great-houk/mouse-project/mouse/max32625-rs/src/clkman/sys_clk_ctrl_10_i2cs.rs

#[doc = "Register `SYS_CLK_CTRL_10_I2CS` reader"]
pub struct R(crate::R<SYS_CLK_CTRL_10_I2CS_SPEC>);
impl core::ops::Deref for R {
    type Target = crate::R<SYS_CLK_CTRL_10_I2CS_SPEC>;
    #[inline(always)]
    fn deref(&self) -> &Self::Target {
        &self.0
    }
}
impl From<crate::R<SYS_CLK_CTRL_10_I2CS_SPEC>> for R {
    #[inline(always)]
    fn from(reader: crate::R<SYS_CLK_CTRL_10_I2CS_SPEC>) -> Self {
        R(reader)
    }
}
#[doc = "Register `SYS_CLK_CTRL_10_I2CS` writer"]
pub struct W(crate::W<SYS_CLK_CTRL_10_I2CS_SPEC>);
impl core::ops::Deref for W {
    type Target = crate::W<SYS_CLK_CTRL_10_I2CS_SPEC>;
    #[inline(always)]
    fn deref(&self) -> &Self::Target {
        &self.0
    }
}
impl core::ops::DerefMut for W {
    #[inline(always)]
    fn deref_mut(&mut self) -> &mut Self::Target {
        &mut self.0
    }
}
impl From<crate::W<SYS_CLK_CTRL_10_I2CS_SPEC>> for W {
    #[inline(always)]
    fn from(writer: crate::W<SYS_CLK_CTRL_10_I2CS_SPEC>) -> Self {
        W(writer)
    }
}
#[doc = "Field `i2cs_clk_scale` reader - Control Settings for CLK10 - Source Clock for I2C Slave"]
pub type I2CS_CLK_SCALE_R = crate::FieldReader<u8, u8>;
#[doc = "Field `i2cs_clk_scale` writer - Control Settings for CLK10 - Source Clock for I2C Slave"]
pub type I2CS_CLK_SCALE_W<'a> =
    crate::FieldWriter<'a, u32, SYS_CLK_CTRL_10_I2CS_SPEC, u8, u8, 4, 0>;
impl R {
    #[doc = "Bits 0:3 - Control Settings for CLK10 - Source Clock for I2C Slave"]
    #[inline(always)]
    pub fn i2cs_clk_scale(&self) -> I2CS_CLK_SCALE_R {
        I2CS_CLK_SCALE_R::new((self.bits & 0x0f) as u8)
    }
}
impl W {
    #[doc = "Bits 0:3 - Control Settings for CLK10 - Source Clock for I2C Slave"]
    #[inline(always)]
    pub fn i2cs_clk_scale(&mut self) -> I2CS_CLK_SCALE_W {
        I2CS_CLK_SCALE_W::new(self)
    }
    #[doc = "Writes raw bits to the register."]
    #[inline(always)]
    pub unsafe fn bits(&mut self, bits: u32) -> &mut Self {
        self.0.bits(bits);
        self
    }
}
#[doc = "Control Settings for CLK10 - Source Clock for I2C Slave\n\nThis register you can [`read`](crate::generic::Reg::read), [`write_with_zero`](crate::generic::Reg::write_with_zero), [`reset`](crate::generic::Reg::reset), [`write`](crate::generic::Reg::write), [`modify`](crate::generic::Reg::modify). See [API](https://docs.rs/svd2rust/#read--modify--write-api).\n\nFor information about available fields see [sys_clk_ctrl_10_i2cs](index.html) module"]
pub struct SYS_CLK_CTRL_10_I2CS_SPEC;
impl crate::RegisterSpec for SYS_CLK_CTRL_10_I2CS_SPEC {
    type Ux = u32;
}
#[doc = "`read()` method returns [sys_clk_ctrl_10_i2cs::R](R) reader structure"]
impl crate::Readable for SYS_CLK_CTRL_10_I2CS_SPEC {
    type Reader = R;
}
#[doc = "`write(|w| ..)` method takes [sys_clk_ctrl_10_i2cs::W](W) writer structure"]
impl crate::Writable for SYS_CLK_CTRL_10_I2CS_SPEC {
    type Writer = W;
}
#[doc = "`reset()` method sets SYS_CLK_CTRL_10_I2CS to value 0"]
impl crate::Resettable for SYS_CLK_CTRL_10_I2CS_SPEC {
    #[inline(always)]
    fn reset_value() -> Self::Ux {
        0
    }
}
