great-houk/mouse-project/mouse/max32625-rs/src/gpio.rs

#[doc = r"Register block"]
#[repr(C)]
pub struct RegisterBlock {
    #[doc = "0x00 - Port P0 Default (Power-On Reset) Output Drive Mode"]
    pub rst_mode_p0: crate::Reg<rst_mode_p0::RST_MODE_P0_SPEC>,
    #[doc = "0x04 - Port P1 Default (Power-On Reset) Output Drive Mode"]
    pub rst_mode_p1: crate::Reg<rst_mode_p1::RST_MODE_P1_SPEC>,
    #[doc = "0x08 - Port P2 Default (Power-On Reset) Output Drive Mode"]
    pub rst_mode_p2: crate::Reg<rst_mode_p2::RST_MODE_P2_SPEC>,
    #[doc = "0x0c - Port P3 Default (Power-On Reset) Output Drive Mode"]
    pub rst_mode_p3: crate::Reg<rst_mode_p3::RST_MODE_P3_SPEC>,
    #[doc = "0x10 - Port P4 Default (Power-On Reset) Output Drive Mode"]
    pub rst_mode_p4: crate::Reg<rst_mode_p4::RST_MODE_P4_SPEC>,
    #[doc = "0x14 - Port P5 Default (Power-On Reset) Output Drive Mode"]
    pub rst_mode_p5: crate::Reg<rst_mode_p5::RST_MODE_P5_SPEC>,
    #[doc = "0x18 - Port P6 Default (Power-On Reset) Output Drive Mode"]
    pub rst_mode_p6: crate::Reg<rst_mode_p6::RST_MODE_P6_SPEC>,
    #[doc = "0x1c - Port P7 Default (Power-On Reset) Output Drive Mode"]
    pub rst_mode_p7: crate::Reg<rst_mode_p7::RST_MODE_P7_SPEC>,
    #[doc = "0x20 - Port P8 Default (Power-On Reset) Output Drive Mode"]
    pub rst_mode_p8: crate::Reg<rst_mode_p8::RST_MODE_P8_SPEC>,
    _reserved9: [u8; 0x1c],
    #[doc = "0x40 - Port P0 Free for GPIO Operation Flags"]
    pub free_p0: crate::Reg<free_p0::FREE_P0_SPEC>,
    #[doc = "0x44 - Port P1 Free for GPIO Operation Flags"]
    pub free_p1: crate::Reg<free_p1::FREE_P1_SPEC>,
    #[doc = "0x48 - Port P2 Free for GPIO Operation Flags"]
    pub free_p2: crate::Reg<free_p2::FREE_P2_SPEC>,
    #[doc = "0x4c - Port P3 Free for GPIO Operation Flags"]
    pub free_p3: crate::Reg<free_p3::FREE_P3_SPEC>,
    #[doc = "0x50 - Port P4 Free for GPIO Operation Flags"]
    pub free_p4: crate::Reg<free_p4::FREE_P4_SPEC>,
    #[doc = "0x54 - Port P5 Free for GPIO Operation Flags"]
    pub free_p5: crate::Reg<free_p5::FREE_P5_SPEC>,
    #[doc = "0x58 - Port P6 Free for GPIO Operation Flags"]
    pub free_p6: crate::Reg<free_p6::FREE_P6_SPEC>,
    #[doc = "0x5c - Port P7 Free for GPIO Operation Flags"]
    pub free_p7: crate::Reg<free_p7::FREE_P7_SPEC>,
    #[doc = "0x60 - Port P8 Free for GPIO Operation Flags"]
    pub free_p8: crate::Reg<free_p8::FREE_P8_SPEC>,
    _reserved18: [u8; 0x1c],
    #[doc = "0x80 - Port P0 GPIO Output Drive Mode"]
    pub out_mode_p0: crate::Reg<out_mode_p0::OUT_MODE_P0_SPEC>,
    #[doc = "0x84 - Port P1 GPIO Output Drive Mode"]
    pub out_mode_p1: crate::Reg<out_mode_p1::OUT_MODE_P1_SPEC>,
    #[doc = "0x88 - Port P2 GPIO Output Drive Mode"]
    pub out_mode_p2: crate::Reg<out_mode_p2::OUT_MODE_P2_SPEC>,
    #[doc = "0x8c - Port P3 GPIO Output Drive Mode"]
    pub out_mode_p3: crate::Reg<out_mode_p3::OUT_MODE_P3_SPEC>,
    #[doc = "0x90 - Port P4 GPIO Output Drive Mode"]
    pub out_mode_p4: crate::Reg<out_mode_p4::OUT_MODE_P4_SPEC>,
    #[doc = "0x94 - Port P5 GPIO Output Drive Mode"]
    pub out_mode_p5: crate::Reg<out_mode_p5::OUT_MODE_P5_SPEC>,
    #[doc = "0x98 - Port P6 GPIO Output Drive Mode"]
    pub out_mode_p6: crate::Reg<out_mode_p6::OUT_MODE_P6_SPEC>,
    #[doc = "0x9c - Port P7 GPIO Output Drive Mode"]
    pub out_mode_p7: crate::Reg<out_mode_p7::OUT_MODE_P7_SPEC>,
    #[doc = "0xa0 - Port P8 GPIO Output Drive Mode"]
    pub out_mode_p8: crate::Reg<out_mode_p8::OUT_MODE_P8_SPEC>,
    _reserved27: [u8; 0x1c],
    #[doc = "0xc0 - Port P0 GPIO Output Value"]
    pub out_val_p0: crate::Reg<out_val_p0::OUT_VAL_P0_SPEC>,
    #[doc = "0xc4 - Port P1 GPIO Output Value"]
    pub out_val_p1: crate::Reg<out_val_p1::OUT_VAL_P1_SPEC>,
    #[doc = "0xc8 - Port P2 GPIO Output Value"]
    pub out_val_p2: crate::Reg<out_val_p2::OUT_VAL_P2_SPEC>,
    #[doc = "0xcc - Port P3 GPIO Output Value"]
    pub out_val_p3: crate::Reg<out_val_p3::OUT_VAL_P3_SPEC>,
    #[doc = "0xd0 - Port P4 GPIO Output Value"]
    pub out_val_p4: crate::Reg<out_val_p4::OUT_VAL_P4_SPEC>,
    #[doc = "0xd4 - Port P5 GPIO Output Value"]
    pub out_val_p5: crate::Reg<out_val_p5::OUT_VAL_P5_SPEC>,
    #[doc = "0xd8 - Port P6 GPIO Output Value"]
    pub out_val_p6: crate::Reg<out_val_p6::OUT_VAL_P6_SPEC>,
    #[doc = "0xdc - Port P7 GPIO Output Value"]
    pub out_val_p7: crate::Reg<out_val_p7::OUT_VAL_P7_SPEC>,
    #[doc = "0xe0 - Port P8 GPIO Output Value"]
    pub out_val_p8: crate::Reg<out_val_p8::OUT_VAL_P8_SPEC>,
    _reserved36: [u8; 0x1c],
    #[doc = "0x100 - Port P0 GPIO Function Select"]
    pub func_sel_p0: crate::Reg<func_sel_p0::FUNC_SEL_P0_SPEC>,
    #[doc = "0x104 - Port P1 GPIO Function Select"]
    pub func_sel_p1: crate::Reg<func_sel_p1::FUNC_SEL_P1_SPEC>,
    #[doc = "0x108 - Port P2 GPIO Function Select"]
    pub func_sel_p2: crate::Reg<func_sel_p2::FUNC_SEL_P2_SPEC>,
    #[doc = "0x10c - Port P3 GPIO Function Select"]
    pub func_sel_p3: crate::Reg<func_sel_p3::FUNC_SEL_P3_SPEC>,
    #[doc = "0x110 - Port P4 GPIO Function Select"]
    pub func_sel_p4: crate::Reg<func_sel_p4::FUNC_SEL_P4_SPEC>,
    #[doc = "0x114 - Port P5 GPIO Function Select"]
    pub func_sel_p5: crate::Reg<func_sel_p5::FUNC_SEL_P5_SPEC>,
    #[doc = "0x118 - Port P6 GPIO Function Select"]
    pub func_sel_p6: crate::Reg<func_sel_p6::FUNC_SEL_P6_SPEC>,
    #[doc = "0x11c - Port P7 GPIO Function Select"]
    pub func_sel_p7: crate::Reg<func_sel_p7::FUNC_SEL_P7_SPEC>,
    #[doc = "0x120 - Port P8 GPIO Function Select"]
    pub func_sel_p8: crate::Reg<func_sel_p8::FUNC_SEL_P8_SPEC>,
    _reserved45: [u8; 0x1c],
    #[doc = "0x140 - Port P0 GPIO Input Monitoring Mode"]
    pub in_mode_p0: crate::Reg<in_mode_p0::IN_MODE_P0_SPEC>,
    #[doc = "0x144 - Port P1 GPIO Input Monitoring Mode"]
    pub in_mode_p1: crate::Reg<in_mode_p1::IN_MODE_P1_SPEC>,
    #[doc = "0x148 - Port P2 GPIO Input Monitoring Mode"]
    pub in_mode_p2: crate::Reg<in_mode_p2::IN_MODE_P2_SPEC>,
    #[doc = "0x14c - Port P3 GPIO Input Monitoring Mode"]
    pub in_mode_p3: crate::Reg<in_mode_p3::IN_MODE_P3_SPEC>,
    #[doc = "0x150 - Port P4 GPIO Input Monitoring Mode"]
    pub in_mode_p4: crate::Reg<in_mode_p4::IN_MODE_P4_SPEC>,
    #[doc = "0x154 - Port P5 GPIO Input Monitoring Mode"]
    pub in_mode_p5: crate::Reg<in_mode_p5::IN_MODE_P5_SPEC>,
    #[doc = "0x158 - Port P6 GPIO Input Monitoring Mode"]
    pub in_mode_p6: crate::Reg<in_mode_p6::IN_MODE_P6_SPEC>,
    #[doc = "0x15c - Port P7 GPIO Input Monitoring Mode"]
    pub in_mode_p7: crate::Reg<in_mode_p7::IN_MODE_P7_SPEC>,
    #[doc = "0x160 - Port P8 GPIO Input Monitoring Mode"]
    pub in_mode_p8: crate::Reg<in_mode_p8::IN_MODE_P8_SPEC>,
    _reserved54: [u8; 0x1c],
    #[doc = "0x180 - Port P0 GPIO Input Value"]
    pub in_val_p0: crate::Reg<in_val_p0::IN_VAL_P0_SPEC>,
    #[doc = "0x184 - Port P1 GPIO Input Value"]
    pub in_val_p1: crate::Reg<in_val_p1::IN_VAL_P1_SPEC>,
    #[doc = "0x188 - Port P2 GPIO Input Value"]
    pub in_val_p2: crate::Reg<in_val_p2::IN_VAL_P2_SPEC>,
    #[doc = "0x18c - Port P3 GPIO Input Value"]
    pub in_val_p3: crate::Reg<in_val_p3::IN_VAL_P3_SPEC>,
    #[doc = "0x190 - Port P4 GPIO Input Value"]
    pub in_val_p4: crate::Reg<in_val_p4::IN_VAL_P4_SPEC>,
    #[doc = "0x194 - Port P5 GPIO Input Value"]
    pub in_val_p5: crate::Reg<in_val_p5::IN_VAL_P5_SPEC>,
    #[doc = "0x198 - Port P6 GPIO Input Value"]
    pub in_val_p6: crate::Reg<in_val_p6::IN_VAL_P6_SPEC>,
    #[doc = "0x19c - Port P7 GPIO Input Value"]
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
pub type INTEN_P7 = crate::Reg<inten_p7::INTEN_P7_SPEC>;
#[doc = "Port P7 Interrupt Enables"]
pub mod inten_p7;
#[doc = "INTEN_P8 register accessor: an alias for `Reg<INTEN_P8_SPEC>`"]
pub type INTEN_P8 = crate::Reg<inten_p8::INTEN_P8_SPEC>;
#[doc = "Port P8 Interrupt Enables"]
pub mod inten_p8;
