great-houk/mouse-project/mouse/max32625-rs/src/gpio/in_mode_p0.rs

#[doc = "Register `IN_MODE_P0` reader"]
pub struct R(crate::R<IN_MODE_P0_SPEC>);
impl core::ops::Deref for R {
    type Target = crate::R<IN_MODE_P0_SPEC>;
    #[inline(always)]
    fn deref(&self) -> &Self::Target {
        &self.0
    }
}
impl From<crate::R<IN_MODE_P0_SPEC>> for R {
    #[inline(always)]
    fn from(reader: crate::R<IN_MODE_P0_SPEC>) -> Self {
        R(reader)
    }
}
#[doc = "Register `IN_MODE_P0` writer"]
pub struct W(crate::W<IN_MODE_P0_SPEC>);
impl core::ops::Deref for W {
    type Target = crate::W<IN_MODE_P0_SPEC>;
    #[inline(always)]
    fn deref(&self) -> &Self::Target {
        &self.0
    }
}
impl core::ops::DerefMut for W {
    #[inline(always)]
    fn deref_mut(&mut self) -> &mut Self::Target {
        &mut self.0
    }
}
impl From<crate::W<IN_MODE_P0_SPEC>> for W {
    #[inline(always)]
    fn from(writer: crate::W<IN_MODE_P0_SPEC>) -> Self {
        W(writer)
    }
}
#[doc = "Field `pin0` reader - P0.0 Input Monitoring Mode"]
pub type PIN0_R = crate::FieldReader<u8, u8>;
#[doc = "Field `pin0` writer - P0.0 Input Monitoring Mode"]
pub type PIN0_W<'a> = crate::FieldWriter<'a, u32, IN_MODE_P0_SPEC, u8, u8, 2, 0>;
#[doc = "Field `pin1` reader - P0.1 Input Monitoring Mode"]
pub type PIN1_R = crate::FieldReader<u8, u8>;
#[doc = "Field `pin1` writer - P0.1 Input Monitoring Mode"]
pub type PIN1_W<'a> = crate::FieldWriter<'a, u32, IN_MODE_P0_SPEC, u8, u8, 2, 4>;
#[doc = "Field `pin2` reader - P0.2 Input Monitoring Mode"]
pub type PIN2_R = crate::FieldReader<u8, u8>;
#[doc = "Field `pin2` writer - P0.2 Input Monitoring Mode"]
pub type PIN2_W<'a> = crate::FieldWriter<'a, u32, IN_MODE_P0_SPEC, u8, u8, 2, 8>;
#[doc = "Field `pin3` reader - P0.3 Input Monitoring Mode"]
pub type PIN3_R = crate::FieldReader<u8, u8>;
#[doc = "Field `pin3` writer - P0.3 Input Monitoring Mode"]
pub type PIN3_W<'a> = crate::FieldWriter<'a, u32, IN_MODE_P0_SPEC, u8, u8, 2, 12>;
#[doc = "Field `pin4` reader - P0.4 Input Monitoring Mode"]
pub type PIN4_R = crate::FieldReader<u8, u8>;
#[doc = "Field `pin4` writer - P0.4 Input Monitoring Mode"]
pub type PIN4_W<'a> = crate::FieldWriter<'a, u32, IN_MODE_P0_SPEC, u8, u8, 2, 16>;
#[doc = "Field `pin5` reader - P0.5 Input Monitoring Mode"]
pub type PIN5_R = crate::FieldReader<u8, u8>;
#[doc = "Field `pin5` writer - P0.5 Input Monitoring Mode"]
pub type PIN5_W<'a> = crate::FieldWriter<'a, u32, IN_MODE_P0_SPEC, u8, u8, 2, 20>;
#[doc = "Field `pin6` reader - P0.6 Input Monitoring Mode"]
pub type PIN6_R = crate::FieldReader<u8, u8>;
#[doc = "Field `pin6` writer - P0.6 Input Monitoring Mode"]
pub type PIN6_W<'a> = crate::FieldWriter<'a, u32, IN_MODE_P0_SPEC, u8, u8, 2, 24>;
#[doc = "Field `pin7` reader - P0.7 Input Monitoring Mode"]
pub type PIN7_R = crate::FieldReader<u8, u8>;
#[doc = "Field `pin7` writer - P0.7 Input Monitoring Mode"]
pub type PIN7_W<'a> = crate::FieldWriter<'a, u32, IN_MODE_P0_SPEC, u8, u8, 2, 28>;
impl R {
    #[doc = "Bits 0:1 - P0.0 Input Monitoring Mode"]
    #[inline(always)]
    pub fn pin0(&self) -> PIN0_R {
        PIN0_R::new((self.bits & 3) as u8)
    }
    #[doc = "Bits 4:5 - P0.1 Input Monitoring Mode"]
    #[inline(always)]
    pub fn pin1(&self) -> PIN1_R {
        PIN1_R::new(((self.bits >> 4) & 3) as u8)
    }
    #[doc = "Bits 8:9 - P0.2 Input Monitoring Mode"]
    #[inline(always)]
    pub fn pin2(&self) -> PIN2_R {
        PIN2_R::new(((self.bits >> 8) & 3) as u8)
    }
    #[doc = "Bits 12:13 - P0.3 Input Monitoring Mode"]
    #[inline(always)]
    pub fn pin3(&self) -> PIN3_R {
        PIN3_R::new(((self.bits >> 12) & 3) as u8)
    }
    #[doc = "Bits 16:17 - P0.4 Input Monitoring Mode"]
    #[inline(always)]
    pub fn pin4(&self) -> PIN4_R {
        PIN4_R::new(((self.bits >> 16) & 3) as u8)
    }
    #[doc = "Bits 20:21 - P0.5 Input Monitoring Mode"]
    #[inline(always)]
    pub fn pin5(&self) -> PIN5_R {
        PIN5_R::new(((self.bits >> 20) & 3) as u8)
    }
    #[doc = "Bits 24:25 - P0.6 Input Monitoring Mode"]
    #[inline(always)]
    pub fn pin6(&self) -> PIN6_R {
        PIN6_R::new(((self.bits >> 24) & 3) as u8)
    }
    #[doc = "Bits 28:29 - P0.7 Input Monitoring Mode"]
    #[inline(always)]
    pub fn pin7(&self) -> PIN7_R {
        PIN7_R::new(((self.bits >> 28) & 3) as u8)
    }
}
impl W {
    #[doc = "Bits 0:1 - P0.0 Input Monitoring Mode"]
    #[inline(always)]
    pub fn pin0(&mut self) -> PIN0_W {
        PIN0_W::new(self)
    }
    #[doc = "Bits 4:5 - P0.1 Input Monitoring Mode"]
    #[inline(always)]
    pub fn pin1(&mut self) -> PIN1_W {
        PIN1_W::new(self)
    }
    #[doc = "Bits 8:9 - P0.2 Input Monitoring Mode"]
    #[inline(always)]
    pub fn pin2(&mut self) -> PIN2_W {
        PIN2_W::new(self)
    }
    #[doc = "Bits 12:13 - P0.3 Input Monitoring Mode"]
    #[inline(always)]
    pub fn pin3(&mut self) -> PIN3_W {
        PIN3_W::new(self)
    }
    #[doc = "Bits 16:17 - P0.4 Input Monitoring Mode"]
    #[inline(always)]
    pub fn pin4(&mut self) -> PIN4_W {
        PIN4_W::new(self)
    }
    #[doc = "Bits 20:21 - P0.5 Input Monitoring Mode"]
    #[inline(always)]
    pub fn pin5(&mut self) -> PIN5_W {
        PIN5_W::new(self)
    }
    #[doc = "Bits 24:25 - P0.6 Input Monitoring Mode"]
    #[inline(always)]
    pub fn pin6(&mut self) -> PIN6_W {
        PIN6_W::new(self)
    }
    #[doc = "Bits 28:29 - P0.7 Input Monitoring Mode"]
    #[inline(always)]
    pub fn pin7(&mut self) -> PIN7_W {
        PIN7_W::new(self)
    }
    #[doc = "Writes raw bits to the register."]
    #[inline(always)]
    pub unsafe fn bits(&mut self, bits: u32) -> &mut Self {
        self.0.bits(bits);
        self
    }
}
#[doc = "Port P0 GPIO Input Monitoring Mode\n\nThis register you can [`read`](crate::generic::Reg::read), [`write_with_zero`](crate::generic::Reg::write_with_zero), [`reset`](crate::generic::Reg::reset), [`write`](crate::generic::Reg::write), [`modify`](crate::generic::Reg::modify). See [API](https://docs.rs/svd2rust/#read--modify--write-api).\n\nFor information about available fields see [in_mode_p0](index.html) module"]
pub struct IN_MODE_P0_SPEC;
impl crate::RegisterSpec for IN_MODE_P0_SPEC {
    type Ux = u32;
}
#[doc = "`read()` method returns [in_mode_p0::R](R) reader structure"]
impl crate::Readable for IN_MODE_P0_SPEC {
    type Reader = R;
}
#[doc = "`write(|w| ..)` method takes [in_mode_p0::W](W) writer structure"]
impl crate::Writable for IN_MODE_P0_SPEC {
    type Writer = W;
}
#[doc = "`reset()` method sets IN_MODE_P0 to value 0"]
impl crate::Resettable for IN_MODE_P0_SPEC {
    #[inline(always)]
    fn reset_value() -> Self::Ux {
        0
    }
}
