great-houk/mouse-project/mouse/max32625-rs/src/gpio/int_mode_p0.rs

#[doc = "Register `INT_MODE_P0` reader"]
pub struct R(crate::R<INT_MODE_P0_SPEC>);
impl core::ops::Deref for R {
    type Target = crate::R<INT_MODE_P0_SPEC>;
    #[inline(always)]
    fn deref(&self) -> &Self::Target {
        &self.0
    }
}
impl From<crate::R<INT_MODE_P0_SPEC>> for R {
    #[inline(always)]
    fn from(reader: crate::R<INT_MODE_P0_SPEC>) -> Self {
        R(reader)
    }
}
#[doc = "Register `INT_MODE_P0` writer"]
pub struct W(crate::W<INT_MODE_P0_SPEC>);
impl core::ops::Deref for W {
    type Target = crate::W<INT_MODE_P0_SPEC>;
    #[inline(always)]
    fn deref(&self) -> &Self::Target {
        &self.0
    }
}
impl core::ops::DerefMut for W {
    #[inline(always)]
    fn deref_mut(&mut self) -> &mut Self::Target {
        &mut self.0
    }
}
impl From<crate::W<INT_MODE_P0_SPEC>> for W {
    #[inline(always)]
    fn from(writer: crate::W<INT_MODE_P0_SPEC>) -> Self {
        W(writer)
    }
}
#[doc = "Field `pin0` reader - P0.0 GPIO Interrupt Detection Mode"]
pub type PIN0_R = crate::FieldReader<u8, u8>;
#[doc = "Field `pin0` writer - P0.0 GPIO Interrupt Detection Mode"]
pub type PIN0_W<'a> = crate::FieldWriter<'a, u32, INT_MODE_P0_SPEC, u8, u8, 3, 0>;
#[doc = "Field `pin1` reader - P0.1 GPIO Interrupt Detection Mode"]
pub type PIN1_R = crate::FieldReader<u8, u8>;
#[doc = "Field `pin1` writer - P0.1 GPIO Interrupt Detection Mode"]
pub type PIN1_W<'a> = crate::FieldWriter<'a, u32, INT_MODE_P0_SPEC, u8, u8, 3, 4>;
#[doc = "Field `pin2` reader - P0.2 GPIO Interrupt Detection Mode"]
pub type PIN2_R = crate::FieldReader<u8, u8>;
#[doc = "Field `pin2` writer - P0.2 GPIO Interrupt Detection Mode"]
pub type PIN2_W<'a> = crate::FieldWriter<'a, u32, INT_MODE_P0_SPEC, u8, u8, 3, 8>;
#[doc = "Field `pin3` reader - P0.3 GPIO Interrupt Detection Mode"]
pub type PIN3_R = crate::FieldReader<u8, u8>;
#[doc = "Field `pin3` writer - P0.3 GPIO Interrupt Detection Mode"]
pub type PIN3_W<'a> = crate::FieldWriter<'a, u32, INT_MODE_P0_SPEC, u8, u8, 3, 12>;
#[doc = "Field `pin4` reader - P0.4 GPIO Interrupt Detection Mode"]
pub type PIN4_R = crate::FieldReader<u8, u8>;
#[doc = "Field `pin4` writer - P0.4 GPIO Interrupt Detection Mode"]
pub type PIN4_W<'a> = crate::FieldWriter<'a, u32, INT_MODE_P0_SPEC, u8, u8, 3, 16>;
#[doc = "Field `pin5` reader - P0.5 GPIO Interrupt Detection Mode"]
pub type PIN5_R = crate::FieldReader<u8, u8>;
#[doc = "Field `pin5` writer - P0.5 GPIO Interrupt Detection Mode"]
pub type PIN5_W<'a> = crate::FieldWriter<'a, u32, INT_MODE_P0_SPEC, u8, u8, 3, 20>;
#[doc = "Field `pin6` reader - P0.6 GPIO Interrupt Detection Mode"]
pub type PIN6_R = crate::FieldReader<u8, u8>;
#[doc = "Field `pin6` writer - P0.6 GPIO Interrupt Detection Mode"]
pub type PIN6_W<'a> = crate::FieldWriter<'a, u32, INT_MODE_P0_SPEC, u8, u8, 3, 24>;
#[doc = "Field `pin7` reader - P0.7 GPIO Interrupt Detection Mode"]
pub type PIN7_R = crate::FieldReader<u8, u8>;
#[doc = "Field `pin7` writer - P0.7 GPIO Interrupt Detection Mode"]
pub type PIN7_W<'a> = crate::FieldWriter<'a, u32, INT_MODE_P0_SPEC, u8, u8, 3, 28>;
impl R {
    #[doc = "Bits 0:2 - P0.0 GPIO Interrupt Detection Mode"]
    #[inline(always)]
    pub fn pin0(&self) -> PIN0_R {
        PIN0_R::new((self.bits & 7) as u8)
    }
    #[doc = "Bits 4:6 - P0.1 GPIO Interrupt Detection Mode"]
    #[inline(always)]
    pub fn pin1(&self) -> PIN1_R {
        PIN1_R::new(((self.bits >> 4) & 7) as u8)
    }
    #[doc = "Bits 8:10 - P0.2 GPIO Interrupt Detection Mode"]
    #[inline(always)]
    pub fn pin2(&self) -> PIN2_R {
        PIN2_R::new(((self.bits >> 8) & 7) as u8)
    }
    #[doc = "Bits 12:14 - P0.3 GPIO Interrupt Detection Mode"]
    #[inline(always)]
    pub fn pin3(&self) -> PIN3_R {
        PIN3_R::new(((self.bits >> 12) & 7) as u8)
    }
    #[doc = "Bits 16:18 - P0.4 GPIO Interrupt Detection Mode"]
    #[inline(always)]
    pub fn pin4(&self) -> PIN4_R {
        PIN4_R::new(((self.bits >> 16) & 7) as u8)
    }
    #[doc = "Bits 20:22 - P0.5 GPIO Interrupt Detection Mode"]
    #[inline(always)]
    pub fn pin5(&self) -> PIN5_R {
        PIN5_R::new(((self.bits >> 20) & 7) as u8)
    }
    #[doc = "Bits 24:26 - P0.6 GPIO Interrupt Detection Mode"]
    #[inline(always)]
    pub fn pin6(&self) -> PIN6_R {
        PIN6_R::new(((self.bits >> 24) & 7) as u8)
    }
    #[doc = "Bits 28:30 - P0.7 GPIO Interrupt Detection Mode"]
    #[inline(always)]
    pub fn pin7(&self) -> PIN7_R {
        PIN7_R::new(((self.bits >> 28) & 7) as u8)
    }
}
impl W {
    #[doc = "Bits 0:2 - P0.0 GPIO Interrupt Detection Mode"]
    #[inline(always)]
    pub fn pin0(&mut self) -> PIN0_W {
        PIN0_W::new(self)
    }
    #[doc = "Bits 4:6 - P0.1 GPIO Interrupt Detection Mode"]
    #[inline(always)]
    pub fn pin1(&mut self) -> PIN1_W {
        PIN1_W::new(self)
    }
    #[doc = "Bits 8:10 - P0.2 GPIO Interrupt Detection Mode"]
    #[inline(always)]
    pub fn pin2(&mut self) -> PIN2_W {
        PIN2_W::new(self)
    }
    #[doc = "Bits 12:14 - P0.3 GPIO Interrupt Detection Mode"]
    #[inline(always)]
    pub fn pin3(&mut self) -> PIN3_W {
        PIN3_W::new(self)
    }
    #[doc = "Bits 16:18 - P0.4 GPIO Interrupt Detection Mode"]
    #[inline(always)]
    pub fn pin4(&mut self) -> PIN4_W {
        PIN4_W::new(self)
    }
    #[doc = "Bits 20:22 - P0.5 GPIO Interrupt Detection Mode"]
    #[inline(always)]
    pub fn pin5(&mut self) -> PIN5_W {
        PIN5_W::new(self)
    }
    #[doc = "Bits 24:26 - P0.6 GPIO Interrupt Detection Mode"]
    #[inline(always)]
    pub fn pin6(&mut self) -> PIN6_W {
        PIN6_W::new(self)
    }
    #[doc = "Bits 28:30 - P0.7 GPIO Interrupt Detection Mode"]
    #[inline(always)]
    pub fn pin7(&mut self) -> PIN7_W {
        PIN7_W::new(self)
    }
    #[doc = "Writes raw bits to the register."]
    #[inline(always)]
    pub unsafe fn bits(&mut self, bits: u32) -> &mut Self {
        self.0.bits(bits);
        self
    }
}
#[doc = "Port P0 Interrupt Detection Mode\n\nThis register you can [`read`](crate::generic::Reg::read), [`write_with_zero`](crate::generic::Reg::write_with_zero), [`reset`](crate::generic::Reg::reset), [`write`](crate::generic::Reg::write), [`modify`](crate::generic::Reg::modify). See [API](https://docs.rs/svd2rust/#read--modify--write-api).\n\nFor information about available fields see [int_mode_p0](index.html) module"]
pub struct INT_MODE_P0_SPEC;
impl crate::RegisterSpec for INT_MODE_P0_SPEC {
    type Ux = u32;
}
#[doc = "`read()` method returns [int_mode_p0::R](R) reader structure"]
impl crate::Readable for INT_MODE_P0_SPEC {
    type Reader = R;
}
#[doc = "`write(|w| ..)` method takes [int_mode_p0::W](W) writer structure"]
impl crate::Writable for INT_MODE_P0_SPEC {
    type Writer = W;
}
#[doc = "`reset()` method sets INT_MODE_P0 to value 0"]
impl crate::Resettable for INT_MODE_P0_SPEC {
    #[inline(always)]
    fn reset_value() -> Self::Ux {
        0
    }
}
